Indemsys/Backup-controller_BACKPMAN-v1.0/Software/Regulated_power_source/APP/Parameters/EMBPMAN.ini

[Main]
Version=2

[frmMain: TcxPropertiesStoreComponent]
=
Height=1176
Left=-8
Top=-8
Width=1936

[grid_ParamsTree: TcxPropertiesStoreComponent]
=
SourceDPI=96
Height=466

[grid_Profiles: TcxPropertiesStoreComponent]
=
SourceDPI=96
Height=119
