Indemsys/Backup-controller_BACKPMAN-v1.0/Software/Regulated_power_source/APP/Mem_man.h

#ifndef BACKPMAN10_APP_MEM_MAN_H
  #define BACKPMAN10_APP_MEM_MAN_H


uint32_t       App_create_pool_memry(void);
void*          App_malloc_pending(ULONG size, ULONG wait_option);
void*          App_malloc(size_t size);
void*          App_calloc(size_t num, size_t size);
void           App_free(VOID *block_ptr);
void           App_get_mem_statistic(uint32_t *size, uint32_t *avail_bytes, uint32_t *fragments);
void           Mem_man_log_statistic(void);

#endif // APP_MEM_MAN_H
